Ardunaut2/Kenbak-1-MEGA-Shield/Kenbakuino_MEGA/Buttons.h

#ifndef buttons_h
#define buttons_h


// buttons/switches
// Interacts with the 15 (8 data, 7 control) push-buttons via
// daisy-chained 74HC165's
class Buttons
{
public:
  enum tButtons
  {
    eBit0,
    eBit1,
    eBit2,
    eBit3,
    eBit4,
    eBit5,
    eBit6,
    eBit7,

    eInputClear,
    eAddressDisplay,
    eAddressSet,
    eMemoryRead,
    eMemoryStore,
    eRunStart,
    eRunStop,
    eUnused
  };

  void Init();

  bool GetButtons(word& State, word& NewPressed, bool deBounce);
  bool IsPressed(word BtnState, int Btn);
  bool GetButtonDown(word BtnState, int& Btn);

private:
//  word ShiftIn(int LatchPin, int DataPin, int ClockPin, int BitOrder);
  word Read();
  static byte m_pMap[];
  word m_wPrevState;
  
  word m_wPrevReading;
  unsigned long m_iTransitionTimeMS;
};

extern Buttons buttons;
#endif
